bienesascha/ESPTonUINO32/src/SPIFFSEditor.cpp

#include "SPIFFSEditor.h"
#include <FS.h>

//File: edit.htm.gz, Size: 4151
#define edit_htm_gz_len 5250
const uint8_t edit_htm_gz[] PROGMEM = {
 0x1f, 0x8b, 0x08, 0x08, 0x7d, 0xfa, 0x9c, 0x5c, 0x00, 0x03, 0x65, 0x64,
  0x69, 0x74, 0x2e, 0x68, 0x74, 0x6d, 0x00, 0xc5, 0x1c, 0xe9, 0x7a, 0xda,
  0x48, 0xf2, 0xbf, 0x9f, 0xa2, 0xa3, 0xd9, 0x09, 0x62, 0x38, 0x7d, 0xc4,
  0x93, 0xc1, 0x26, 0x19, 0xc0, 0x76, 0xec, 0xf8, 0x8c, 0xc1, 0xc9, 0x38,
  0xd9, 0xec, 0x7c, 0x42, 0x6a, 0x40, 0xb1, 0x90, 0x14, 0x49, 0x18, 0x48,
  0xd6, 0xef, 0xbe, 0x55, 0x7d, 0x48, 0xad, 0x03, 0xe2, 0x64, 0x66, 0x77,
  0x73, 0x18, 0xd4, 0x5d, 0x55, 0x5d, 0x5d, 0x77, 0x1f, 0xf2, 0xfe, 0x93,
  0x5a, 0x6d, 0x30, 0xb1, 0x43, 0x02, 0xff, 0xa2, 0x09, 0x25, 0xbe, 0x63,
  0xd8, 0x2e, 0x99, 0x44, 0x53, 0x87, 0x84, 0xde, 0x2c, 0x30, 0x29, 0xf1,
  0x46, 0xac, 0x63, 0x42, 0x17, 0x84, 0xba, 0xa6, 0x67, 0x51, 0x8b, 0x1c,
  0x5a, 0x76, 0xe4, 0x05, 0xb5, 0x2b, 0x63, 0x4c, 0x09, 0x9d, 0x0e, 0xa9,
  0x85, 0x8d, 0x80, 0xd6, 0xbf, 0x3a, 0x39, 0x3a, 0xea, 0xf3, 0xde, 0xba,
  0xe9, 0xfb, 0xa4, 0x56, 0x7b, 0xb1, 0xb1, 0xff, 0xe4, 0xe0, 0xb2, 0x37,
  0xb8, 0xbd, 0x3a, 0x64, 0x54, 0xe1, 0x99, 0x11, 0x77, 0x0c, 0x77, 0xdc,
  0xd6, 0xa8, 0xab, 0x61, 0x03, 0x35, 0x2c, 0xf8, 0x88, 0xec, 0xc8, 0xa1,
  0x2f, 0x38, 0xf6, 0x7e, 0x83, 0x3f, 0x6d, 0xec, 0x87, 0xd1, 0xd2, 0xa1,
  0x24, 0x5a, 0xfa, 0xb4, 0xad, 0x45, 0x74, 0x11, 0x35, 0xcc, 0x30, 0xd4,
  0xc8, 0x94, 0x5a, 0xb6, 0xd1, 0xd6, 0x42, 0x33, 0xa0, 0x8c, 0x46, 0xdd,
  0x9c, 0x92, 0xaf, 0x1b, 0x84, 0x7c, 0xa9, 0xd9, 0xae, 0x45, 0x17, 0x2d,
  0xb2, 0xdd, 0x6c, 0xee, 0xc1, 0xb3, 0xef, 0x85, 0x76, 0x64, 0x7b, 0x6e,
  0x8b, 0x18, 0xc3, 0xd0, 0x73, 0x66, 0x11, 0xc5, 0x56, 0x87, 0x8e, 0xa2,
  0x16, 0x79, 0xe6, 0x2f, 0xf0, 0x61, 0xe8, 0x05, 0x16, 0x0d, 0x5a, 0x64,
  0xd3, 0x5f, 0xc0, 0x94, 0x1d, 0xdb, 0x22, 0x3f, 0xed, 0xec, 0xec, 0xb0,
  0x1e, 0xc3, 0xbc, 0x1b, 0x07, 0xde, 0xcc, 0xb5, 0x6a, 0xa6, 0xe7, 0x78,
  0x00, 0xf3, 0xd3, 0xd1, 0x33, 0xfc, 0x8b, 0x9d, 0x96, 0x1d, 0x82, 0xac,
  0x96, 0x2d, 0xe2, 0x7a, 0x2e, 0xe5, 0x74, 0x16, 0xb5, 0x70, 0x62, 0x58,
  0xde, 0xbc, 0x45, 0x9a, 0xf0, 0x77, 0xb3, 0x09, 0x04, 0x83, 0xf1, 0xd0,
  0xd0, 0x49, 0xb3, 0x2a, 0xfe, 0xd5, 0x77, 0x48, 0x19, 0x61, 0x47, 0x9e,
  0x1b, 0xd5, 0x42, 0xfb, 0x0b, 0x85, 0x61, 0xb7, 0x38, 0x1b, 0xac, 0x69,
  0x64, 0x4c, 0x6d, 0x07, 0x68, 0x86, 0x86, 0x1b, 0xd6, 0x42, 0x1a, 0xd8,
  0xa3, 0xb8, 0x6b, 0x4e, 0xed, 0xf1, 0x24, 0x6a, 0x0d, 0x3d, 0xc7, 0xda,
  0xdb, 0x78, 0x60, 0x13, 0x9e, 0x39, 0x6c, 0xce, 0x8e, 0x1d, 0x02, 0x31,
  0x14, 0x53, 0xc2, 0x4c, 0xe4, 0xf9, 0xc0, 0x45, 0x32, 0x57, 0xf6, 0x75,
  0x6a, 0x04, 0x63, 0xdb, 0x15, 0x0f, 0xbe, 0x61, 0x59, 0xb6, 0x3b, 0x66,
  0x4f, 0x9c, 0x9c, 0x63, 0x33, 0x72, 0x89, 0xc8, 0x02, 0xea, 0x18, 0x91,
  0x7d, 0xcf, 0x08, 0x4e, 0x6d, 0xb7, 0x36, 0xb7, 0xad, 0x68, 0xd2, 0x22,
  0xbb, 0x4d, 0xce, 0xb1, 0x39, 0x0b, 0x42, 0x14, 0x8a, 0xef, 0xd9, 0x6e,
  0x44, 0x03, 0x49, 0x26, 0xf4, 0x0d, 0x97, 0x11, 0x92, 0x32, 0x13, 0xd2,
  0x8c, 0x05, 0x66, 0xbb, 0x8e, 0xed, 0xd2, 0xda, 0xd0, 0xf1, 0xcc, 0xbb,
  0x14, 0x27, 0xbb, 0x48, 0x57, 0xf2, 0xd2, 0x9a, 0x78, 0xf7, 0x34, 0x20,
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
};

#define SPIFFS_MAXLENGTH_FILEPATH 32
const char *excludeListFile = "/.exclude.files";

typedef struct ExcludeListS {
    char *item;
    ExcludeListS *next;
} ExcludeList;

static ExcludeList *excludes = NULL;

static bool matchWild(const char *pattern, const char *testee) {
  const char *nxPat = NULL, *nxTst = NULL;

  while (*testee) {
    if (( *pattern == '?' ) || (*pattern == *testee)){
      pattern++;testee++;
      continue;
    }
    if (*pattern=='*'){
      nxPat=pattern++; nxTst=testee;
      continue;
    }
    if (nxPat){ 
      pattern = nxPat+1; testee=++nxTst;
      continue;
    }
    return false;
  }
  while (*pattern=='*'){pattern++;}  
  return (*pattern == 0);
}

static bool addExclude(const char *item){
    size_t len = strlen(item);
    if(!len){
        return false;
    }
    ExcludeList *e = (ExcludeList *)malloc(sizeof(ExcludeList));
    if(!e){
        return false;
    }
    e->item = (char *)malloc(len+1);
    if(!e->item){
        free(e);
        return false;
    }
    memcpy(e->item, item, len+1);
    e->next = excludes;
    excludes = e;
    return true;
}

static void loadExcludeList(fs::FS &_fs, const char *filename){
    static char linebuf[SPIFFS_MAXLENGTH_FILEPATH];
    fs::File excludeFile=_fs.open(filename, "r");
    if(!excludeFile){
        //addExclude("/*.js.gz");
        return;
    }
#ifdef ESP32
    if(excludeFile.isDirectory()){
      excludeFile.close();
      return;
    }
#endif
    if (excludeFile.size() > 0){
      uint8_t idx;
      bool isOverflowed = false;
      while (excludeFile.available()){
        linebuf[0] = '\0';
        idx = 0;
        int lastChar;
        do {
          lastChar = excludeFile.read();
          if(lastChar != '\r'){
            linebuf[idx++] = (char) lastChar;
          }
        } while ((lastChar >= 0) && (lastChar != '\n') && (idx < SPIFFS_MAXLENGTH_FILEPATH));

        if(isOverflowed){
          isOverflowed = (lastChar != '\n');
          continue;
        }
        isOverflowed = (idx >= SPIFFS_MAXLENGTH_FILEPATH);
        linebuf[idx-1] = '\0';
        if(!addExclude(linebuf)){
            excludeFile.close();
            return;
        }
      }
    }
    excludeFile.close();
}

static bool isExcluded(fs::FS &_fs, const char *filename) {
  if(excludes == NULL){
      loadExcludeList(_fs, excludeListFile);
  }
  ExcludeList *e = excludes;
  while(e){
    if (matchWild(e->item, filename)){
      return true;
    }
    e = e->next;
  }
  return false;
}

// WEB HANDLER IMPLEMENTATION

#ifdef ESP32
SPIFFSEditor::SPIFFSEditor(const fs::FS& fs, const String& username, const String& password)
#else
SPIFFSEditor::SPIFFSEditor(const String& username, const String& password, const fs::FS& fs)
#endif
:_fs(fs)
,_username(username)
,_password(password)
,_authenticated(false)
,_startTime(0)
{}

bool SPIFFSEditor::canHandle(AsyncWebServerRequest *request){
  if(request->url().equalsIgnoreCase("/edit")){
    if(request->method() == HTTP_GET){
      if(request->hasParam("list"))
        return true;
      if(request->hasParam("edit")){
        request->_tempFile = _fs.open(request->arg("edit"), "r");
        if(!request->_tempFile){
          return false;
        }
#ifdef ESP32
        if(request->_tempFile.isDirectory()){
          request->_tempFile.close();
          return false;
        }
#endif
      }
      if(request->hasParam("download")){
        request->_tempFile = _fs.open(request->arg("download"), "r");
        if(!request->_tempFile){
          return false;
        }
#ifdef ESP32
        if(request->_tempFile.isDirectory()){
          request->_tempFile.close();
          return false;
        }
#endif
      }
      request->addInterestingHeader("If-Modified-Since");
      return true;
    }
    else if(request->method() == HTTP_POST)
      return true;
    else if(request->method() == HTTP_DELETE)
      return true;
    else if(request->method() == HTTP_PUT)
      return true;

  }
  return false;
}


void SPIFFSEditor::handleRequest(AsyncWebServerRequest *request){
  if(_username.length() && _password.length() && !request->authenticate(_username.c_str(), _password.c_str()))
    return request->requestAuthentication();

  if(request->method() == HTTP_GET){
    if(request->hasParam("list")){
      String path = request->getParam("list")->value();
#ifdef ESP32
      File dir = _fs.open(path);
#else
      Dir dir = _fs.openDir(path);
#endif
      path = String();
      String output = "[";
#ifdef ESP32
      File entry = dir.openNextFile();
      while(entry){
#else
      while(dir.next()){
        fs::File entry = dir.openFile("r");
#endif
        if (isExcluded(_fs, entry.name())) {
#ifdef ESP32
            entry = dir.openNextFile();
#endif
            continue;
        }
        if (output != "[") output += ',';
        output += "{\"type\":\"";
        output += "file";
        output += "\",\"name\":\"";
        output += String(entry.name());
        output += "\",\"size\":";
        output += String(entry.size());
        output += "}";
#ifdef ESP32
        entry = dir.openNextFile();
#else
        entry.close();
#endif
      }
#ifdef ESP32
      dir.close();
#endif
      output += "]";
      request->send(200, "application/json", output);
      output = String();
    }
    else if(request->hasParam("edit") || request->hasParam("download")){
      request->send(request->_tempFile, request->_tempFile.name(), String(), request->hasParam("download"));
    }
    else {
      const char * buildTime = __DATE__ " " __TIME__ " GMT";
      if (request->header("If-Modified-Since").equals(buildTime)) {
        request->send(304);
      } else {
        AsyncWebServerResponse *response = request->beginResponse_P(200, "text/html", edit_htm_gz, edit_htm_gz_len);
        response->addHeader("Content-Encoding", "gzip");
        response->addHeader("Last-Modified", buildTime);
        request->send(response);
      }
    }
  } else if(request->method() == HTTP_DELETE){
    if(request->hasParam("path", true)){
        _fs.remove(request->getParam("path", true)->value());
      request->send(200, "", "DELETE: "+request->getParam("path", true)->value());
    } else
      request->send(404);
  } else if(request->method() == HTTP_POST){
    if(request->hasParam("data", true, true) && _fs.exists(request->getParam("data", true, true)->value()))
      request->send(200, "", "UPLOADED: "+request->getParam("data", true, true)->value());
    else
      request->send(500);
  } else if(request->method() == HTTP_PUT){
    if(request->hasParam("path", true)){
      String filename = request->getParam("path", true)->value();
      if(_fs.exists(filename)){
        request->send(200);
      } else {
        fs::File f = _fs.open(filename, "w");
        if(f){
          f.write((uint8_t)0x00);
          f.close();
          request->send(200, "", "CREATE: "+filename);
        } else {
          request->send(500);
        }
      }
    } else
      request->send(400);
  }
}

void SPIFFSEditor::handleUpload(AsyncWebServerRequest *request, const String& filename, size_t index, uint8_t *data, size_t len, bool final){
  if(!index){
    if(!_username.length() || request->authenticate(_username.c_str(),_password.c_str())){
      _authenticated = true;
      request->_tempFile = _fs.open(filename, "w");
      _startTime = millis();
    }
  }
  if(_authenticated && request->_tempFile){
    if(len){
      request->_tempFile.write(data,len);
    }
    if(final){
      request->_tempFile.close();
    }
  }
}
